LouisLee985/Homekit_ESP_AC_IRemote/src/accessory.h

#ifndef _ACESSORY_H_
#define _ACESSORY_H_

extern homekit_characteristic_t ac_name;
extern homekit_characteristic_t optional_name;
// Thermostat
extern homekit_characteristic_t current_temperature;
extern homekit_characteristic_t current_heater_cooler_state;
extern homekit_characteristic_t target_heater_cooler_state;
extern homekit_characteristic_t current_relative_humidity;
extern homekit_characteristic_t cooling_threshold_temperature;
extern homekit_characteristic_t rotation_speed;
extern homekit_characteristic_t swing_mode;

#endif // _ACESSORY_H_
